seeminglydumbideas-sudo/rack-homelab/rack_10inches/references/Selection_002.png

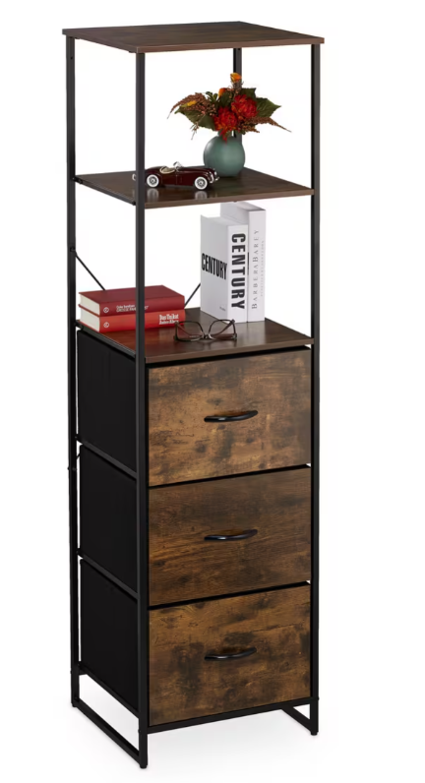
rack_10inches/references/Selection_002.png
