seeminglydumbideas-sudo/rack-homelab/rack_10inches/references/Selection_003.png

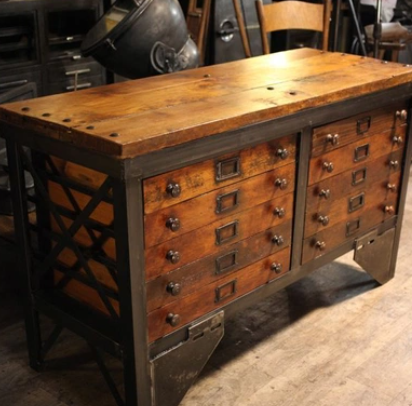
rack_10inches/references/Selection_003.png
