seeminglydumbideas-sudo/rack-homelab/rack_10inches/references/Selection_005.png

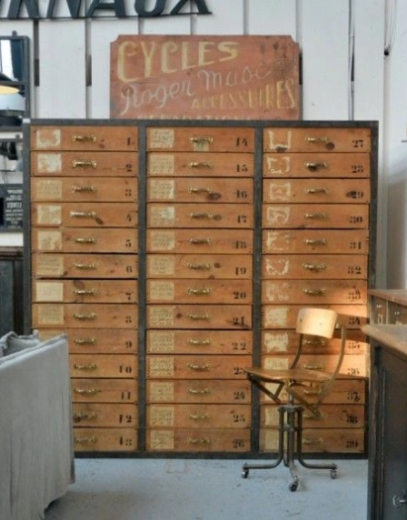
rack_10inches/references/Selection_005.png
