seeminglydumbideas-sudo/rack-homelab/rack_10inches/references/Selection_007.png

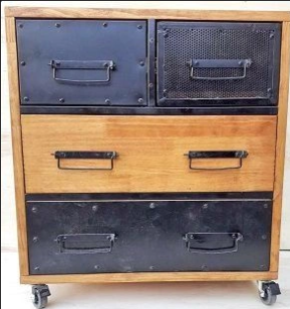
rack_10inches/references/Selection_007.png
