seeminglydumbideas-sudo/rack-homelab/rack_10inches/references/Selection_011.png

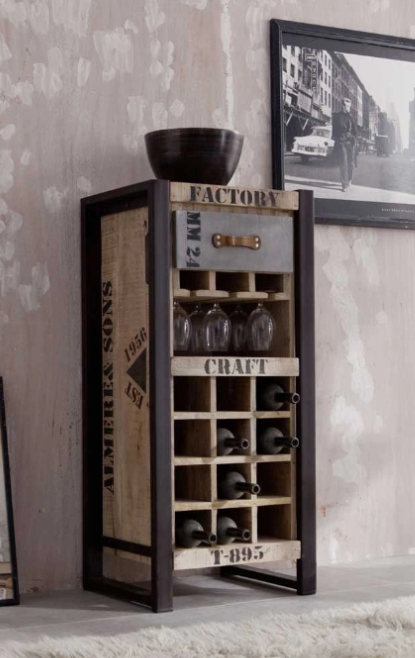
rack_10inches/references/Selection_011.png
