seeminglydumbideas-sudo/rack-homelab/rack_10inches/references/Selection_012.png

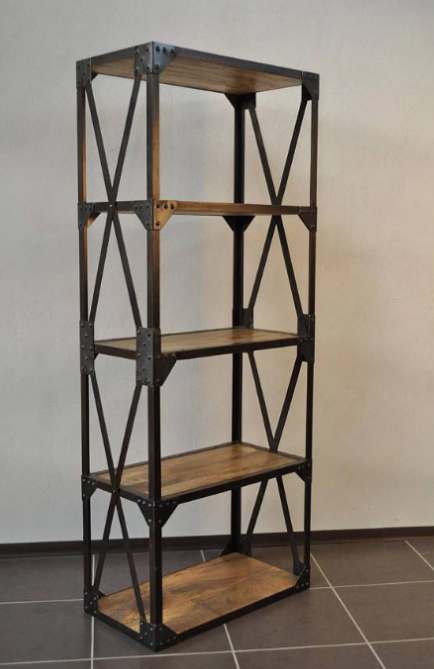
rack_10inches/references/Selection_012.png
