seeminglydumbideas-sudo/rack-homelab/resources/rack 8u_rails-AliExpress.png

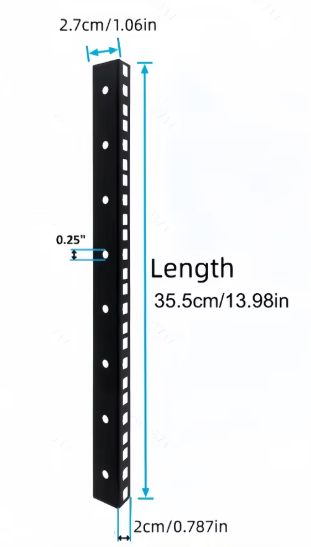
resources/rack 8u_rails-AliExpress.png
