seeminglydumbideas-sudo/rack-homelab/screenshots/rack_assembly.scad — OpenSCAD_001.png

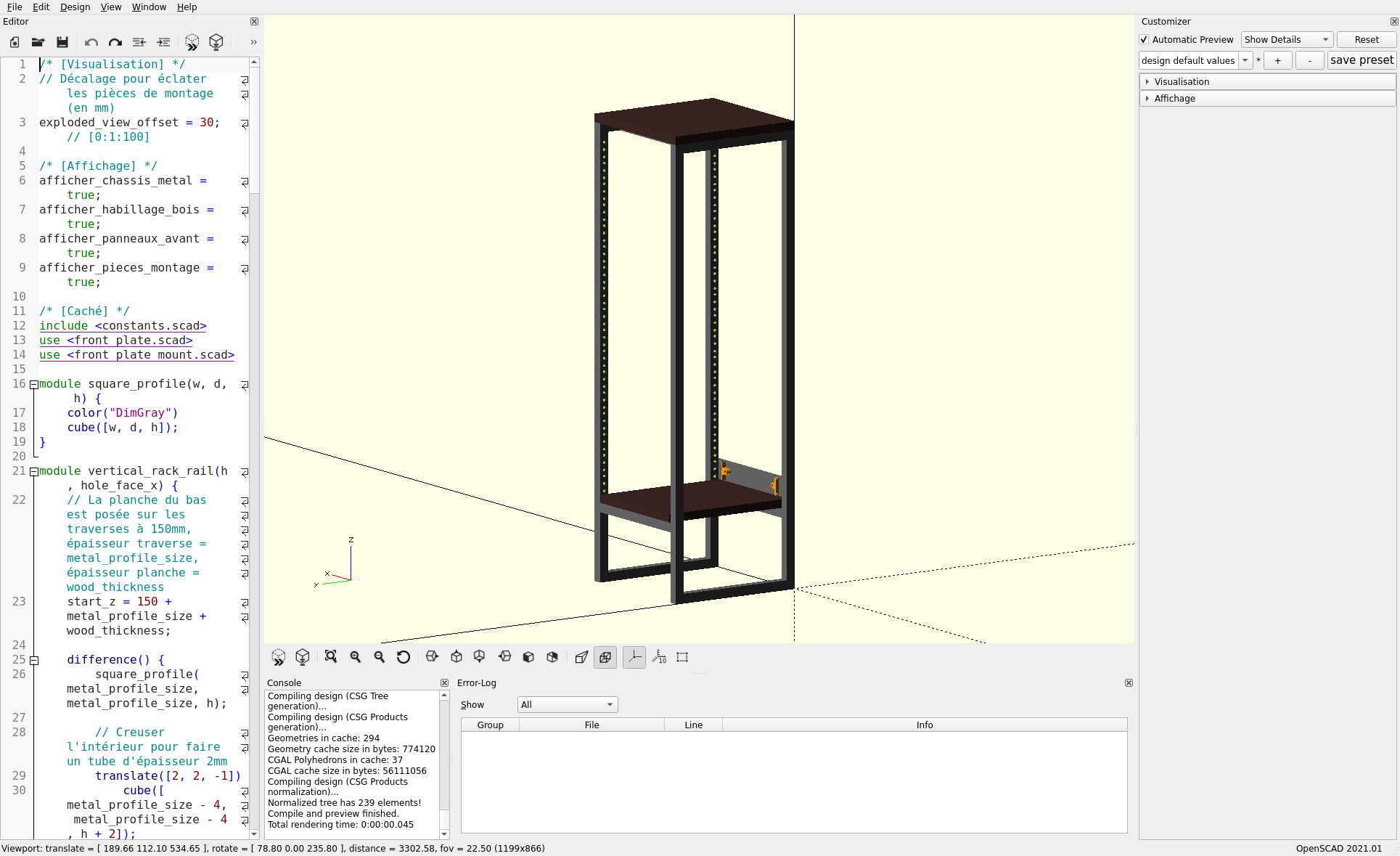
screenshots/rack_assembly.scad — OpenSCAD_001.png
