seeminglydumbideas-sudo/rack-homelab/screenshots/rack_assembly.scad — OpenSCAD_002.png

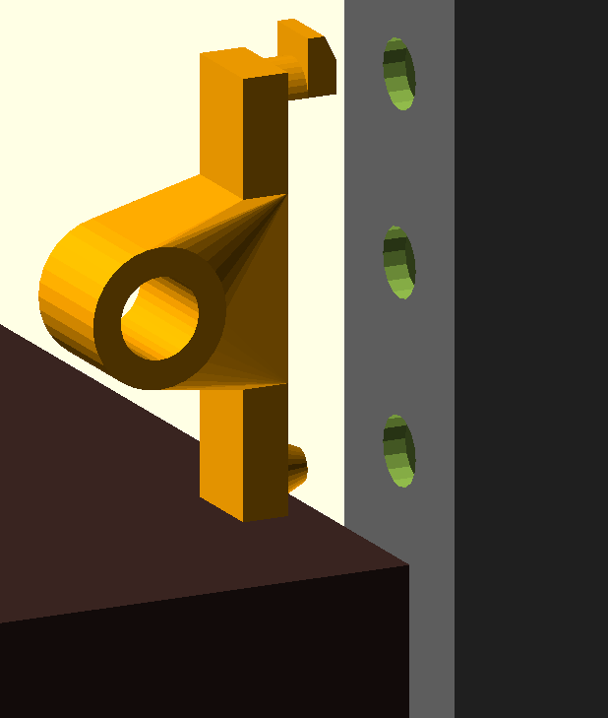
screenshots/rack_assembly.scad — OpenSCAD_002.png
