seeminglydumbideas-sudo/rack-homelab/stackable-3d-prints/main.scad — OpenSCAD_001.png

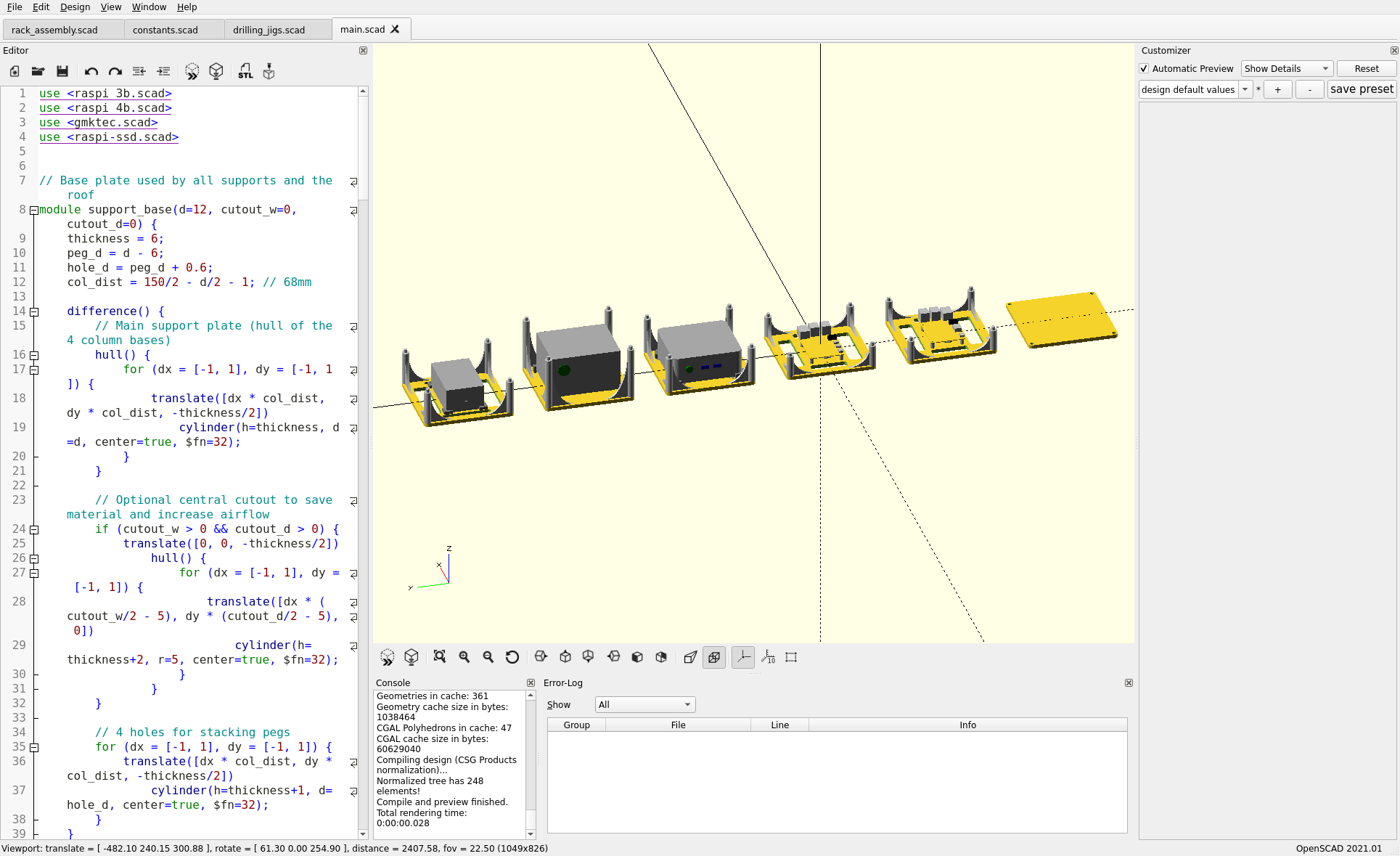
stackable-3d-prints/main.scad — OpenSCAD_001.png
